jAnAnIshreee/Just-Dance-/Resources/LM4041 Voltage Reference Design.xlsx

Goal: design a shunt reference circuit
Jonathan Valvano, EE445L
Desired Vz | 1.5 | volts | 1) pick a desired reference voltage Vz (volts)
Vref | 1.233 | volts | LM4041 parameter
R1 | 47 | kohm | 2) choose a standard resistance value (kohm)
best R2 | 10.17761557 | kohm
Pick R2 | 10 | kohm | 3) pick a standard value for R2 close to best R2
Actual Vref | 1.495340426 | volts | Vz=Vref(1+R2/R1)
Vs | 3.3 | volts | V supply
Rin | 2 | kohm | 4) estimate input impedence on Vz (e.g., to DAC)
Iz | 0.08 | mA | LM4041 parameter
Iref | 0.02623404255 | mA | Vz/(R1+R2), Ohms Law, current through R1,R2
IL | 0.7476702128 | mA | Vz/Rin, Ohms Law, current through Rin
I total | 0.8539042553 | mA | Iz+Iref+IL
max Rs | 2.113421456 | kohm | (Vs-Vz)/Itotal
 |  |  | 5) choose Rs less than max Rs
