jAnAnIshreee/Just-Dance-/Resources/Lab 10/call_graph.png

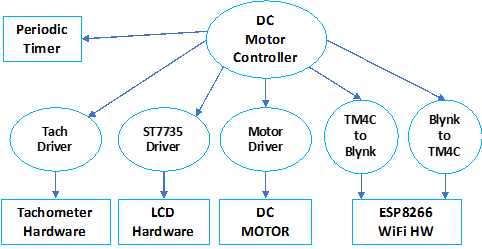
Resources/Lab 10/call_graph.png
