jAnAnIshreee/Just-Dance-/Resources/Lab 10/figure_10.3.png

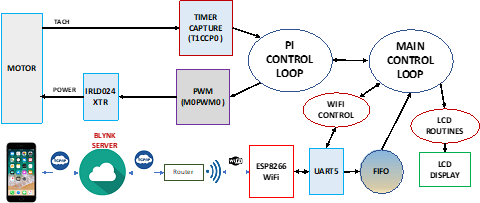
Resources/Lab 10/figure_10.3.png
