jAnAnIshreee/Just-Dance-/Resources/Lab 10/figure_10.7.png

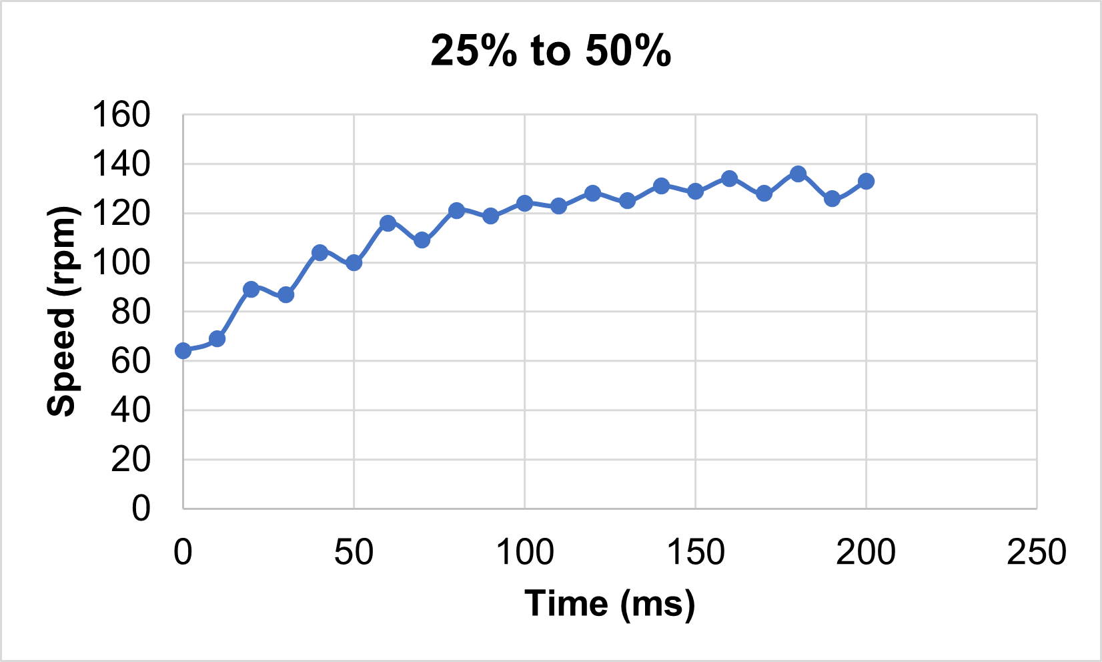
Resources/Lab 10/figure_10.7.png
