jAnAnIshreee/Just-Dance-/Resources/Lab 10/figure_10.9.png

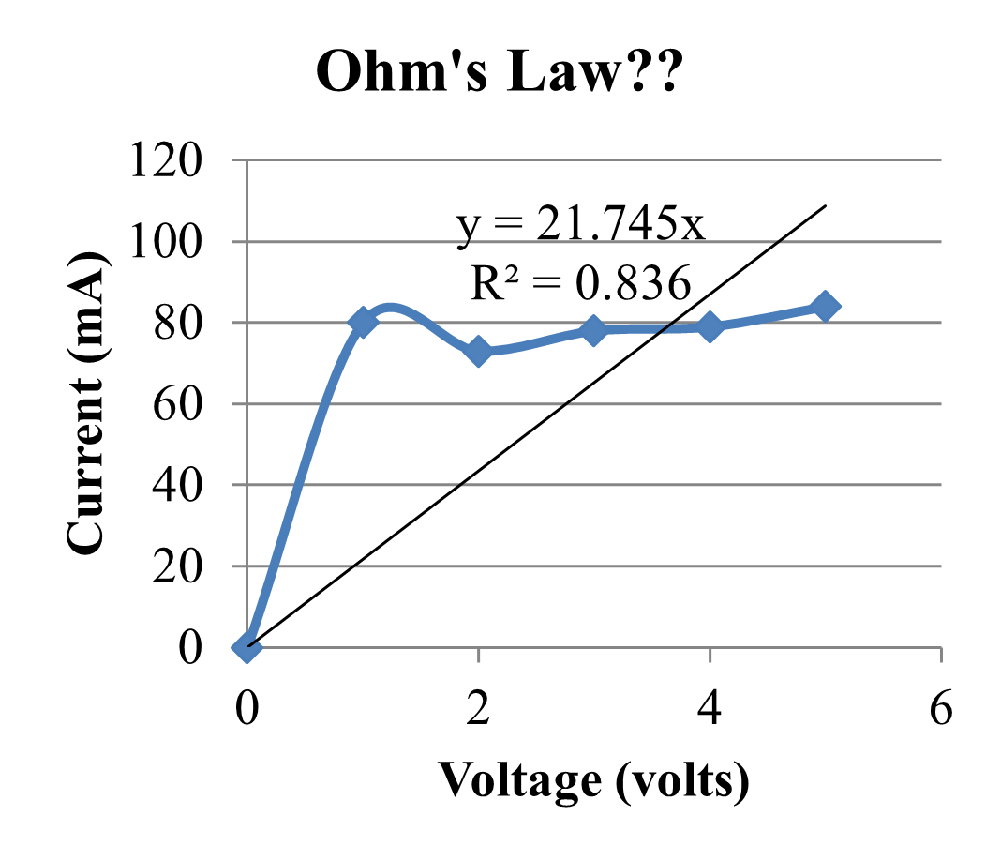
Resources/Lab 10/figure_10.9.png
