jAnAnIshreee/Just-Dance-/Resources/Lab 10/figure_10.10.png

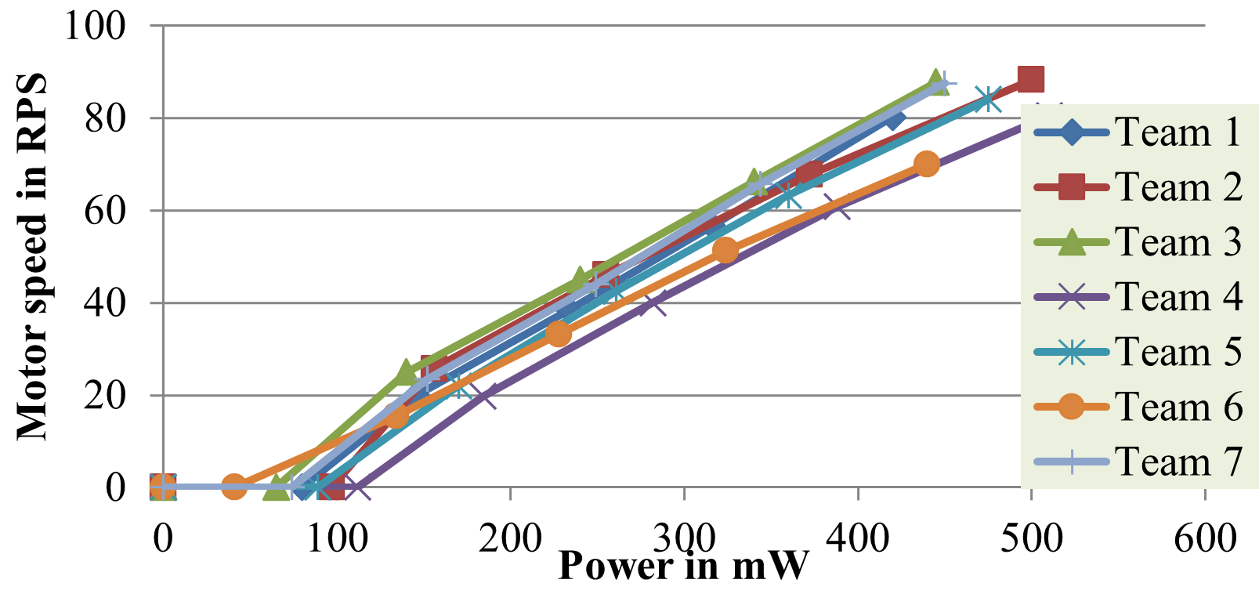
Resources/Lab 10/figure_10.10.png
