jAnAnIshreee/Just-Dance-/Resources/Lab 10/lab_10_block_diagram.png

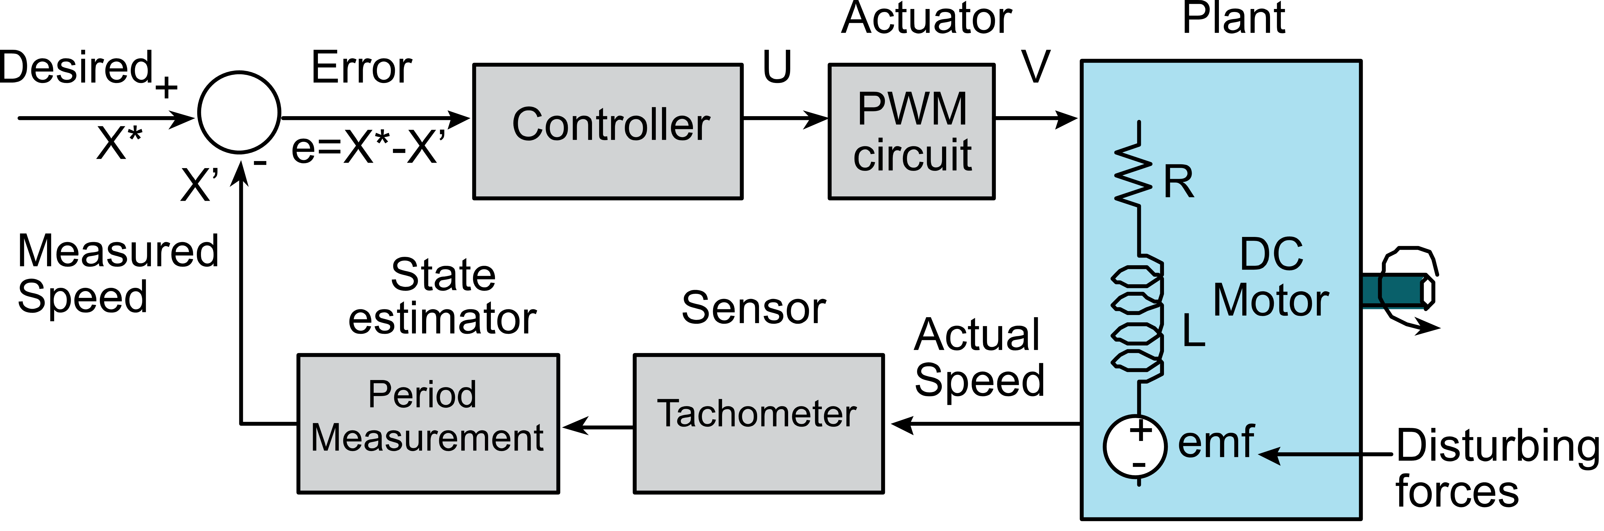
Resources/Lab 10/lab_10_block_diagram.png
