jAnAnIshreee/Just-Dance-/Resources/src/img/kicad_adding_libraries/12.png

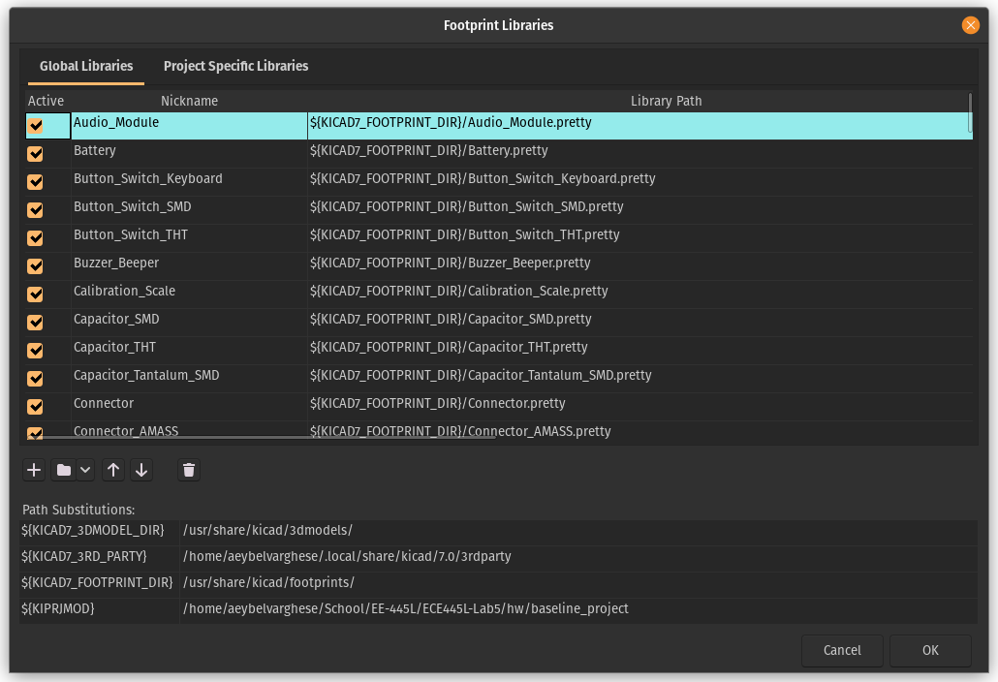
Resources/src/img/kicad_adding_libraries/12.png
