jAnAnIshreee/Just-Dance-/Resources/src/img/kicad_creating_symbols/2.png

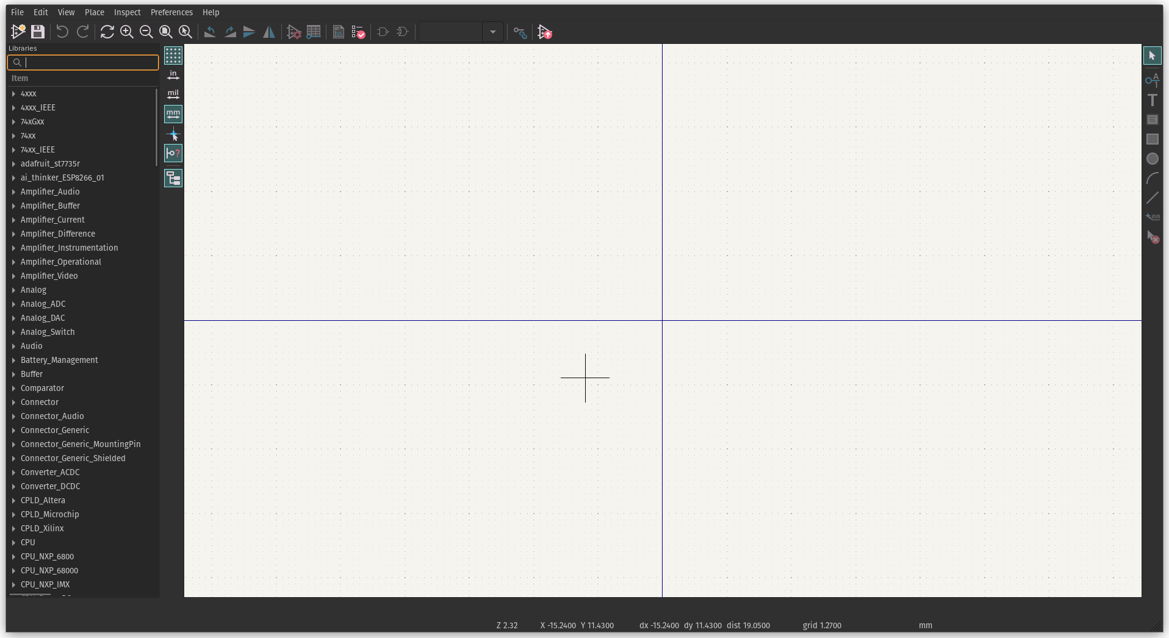
Resources/src/img/kicad_creating_symbols/2.png
